gmittone/arduino-heart/hardware/3d/3d_2.png

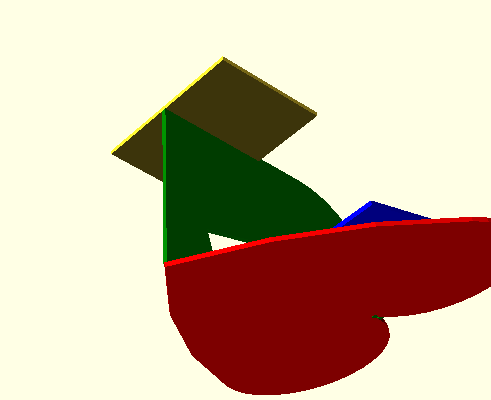
hardware/3d/3d_2.png
