gmittone/arduino-heart/hardware/pcb/heart2.png

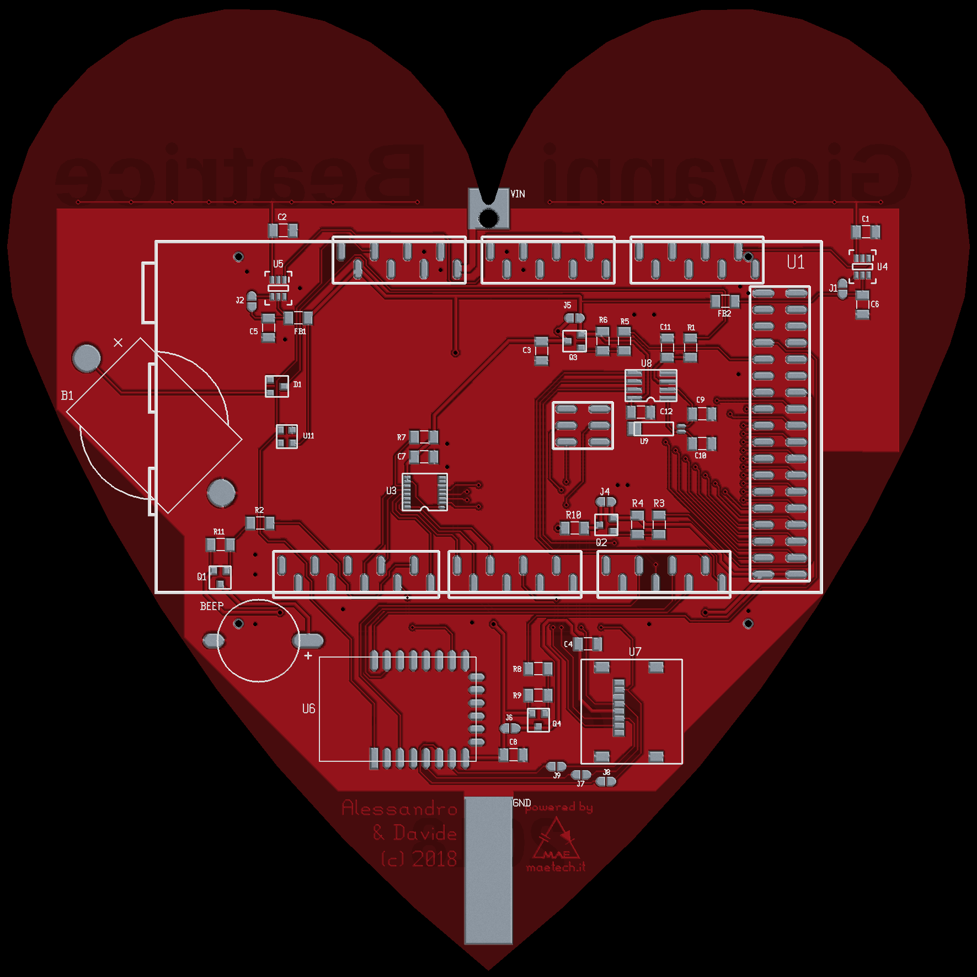
hardware/pcb/heart2.png
