gmittone/arduino-heart/hardware/pcb/stand2_1.png

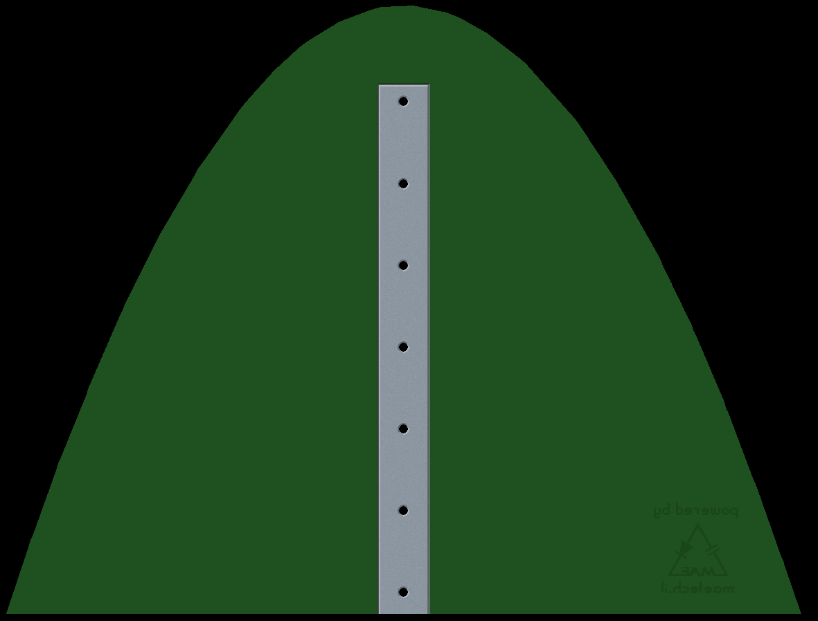
hardware/pcb/stand2_1.png
